HappyShield/happyshield.github.io/index_PT.md

---
layout: page
title: HappyShield
tagline: Curved Crease Origami Face Shield For Infection Control
permalink: /pt/
language: pt
---

<style>.embed-container { position: relative; padding-bottom: 56.25%; height: 0; overflow: hidden; max-width: 100%; } .embed-container iframe, .embed-container object, .embed-container embed { position: absolute; top: 0; left: 0; width: 100%; height: 100%; }</style><div class='embed-container'><iframe src='https://www.youtube.com/embed//NzHtaLhImxM' frameborder='0' allowfullscreen></iframe></div>

---

HappyShieldGif

# What? 

---

HappyShield is a new **open-source** design for a **simple, foldable face shield** for infection control in the context of the Covid-19 pandemic. 

---

# Why?

---

Healthcare workers need face shields in addition to masks and goggles to provide protection from splashes and sprays of infected bodily fluids from Covid-19 patients during a number of high-risk medical procedures and situations. There is currently a **significant shortage of face shields globally**, which is likely to be **particularly severe in less wealthy regions** without the ability to buy or manufacture necessary Personal Protective Equipment (PPE) as easily or quickly as wealthy countries. 

---

# How? 

---

The aim of this project is to develop, disseminate, and mass-manufacture a set of designs for face shields which are **safe**, **cheap**, **easy to mass-produce** quickly using **materials, equipment, and labour available in low and middle-income regions**, are **easy to reuse**, and are **comfortable** enough to be worn for extended periods by healthcare workers without inducing pain or discomfort. The first phase of this project, the development of a prototype design, has yielded **HappyShield**, which successfully meets these design goals. The features of the HappyShield design are listed below:

---

## Features

---

* Single-sheet fluid-impermeable design with **extra protection from fluids and sprays from above**.   

---

* Easy **decontamination for reuse** over high numbers of shifts.   

---

* Form-fitting and adjustable shape allowing for **comfortable wearing for extended periods**.   

---

* **Fast, flexible and scaleable mass-manufacturing approaches** to help meet global demand despite supply chain disruptions.  

---
---

## Gallery

---

<script src="https://snapwidget.com/js/snapwidget.js"></script>
<iframe src="https://snapwidget.com/embed/810063" class="snapwidget-widget" allowtransparency="true" frameborder="0" scrolling="no" style="border:none; overflow:hidden;  width:100%; "></iframe>

---
---

# How can I help? 

---

We have **begun production of HappyShields in the UK**, and are hoping to **rapidly expand** our production and distribution capacity here. Most especially, however, we are **currently seeking partnerships and collaborations** which can help us to disseminate the HappyShield design and related production methods to **less wealthy countries** and jump-start mass-production of face shields there as quickly as possible.

---

### _Here's how you can help:_

---

## 1. 🏭 Manufacturers and Makers

Do you have **access to a laser-cutter, a bench-mounted hydraulic press, die-cutting machinery**, or have connections to an institution or business which does? [We would love to be connected](mailto:natmat@aha.cam.ac.uk?Subject=HappyShield Inquiry: Manufacturing) so that we can help you to **start mass-manufacturing HappyShields locally** as quickly as possible.

Are you a **maker / DIY enthusiast**? We have developed and documented a small number of diverse manufacturing pathways (shown below) for HappyShield, but because of the simplicity of the design, we anticipate there being many effective ways to produce them using locally available materials, equipment, and labor. We need your help to **develop and document these new methods** so that makers and manufacturers worldwide can scale up production using materials and equipment that they already have. All of our [documentation](https://github.com/HappyShield/happyshield.github.io) and [template files](https://github.com/HappyShield/HappyShield) are available open-source on GitHub. Pull requests are encouraged!

---

| Production Method | Web | Print | Video | Templates |
|---|---|---|---|---|
| Hand Creasing | [<i class="em em-iphone" aria-role="presentation" aria-label="MOBILE PHONE"></i>](../hand-creasing/{{page.language}}/) |  [<i class="em em-page_facing_up" aria-role="presentation" aria-label="PAGE FACING UP"></i>](./Instructions/HandCreasing/Assets/Output/InstructionsPDF/Instructions.pdf)  | [<i class="em em-video_camera" aria-role="presentation" aria-label="VIDEO CAMERA"></i>](https://youtu.be/8RvlrtrebBE) | [<i class="em em-triangular_ruler" aria-role="presentation" aria-label="TRIANGULAR RULER"></i>](https://github.com/HappyShield/HappyShield/tree/master/Templates/HandCreasing) |
| Laser-cut + Pressure Creasing | [<i class="em em-iphone" aria-role="presentation" aria-label="MOBILE PHONE"></i>](../pressure-creasing/{{page.language}}/) | [<i class="em em-page_facing_up" aria-role="presentation" aria-label="PAGE FACING UP"></i>](./Instructions/LaserCutAndPressureCreasing/Assets/Output/InstructionsPDF/Instructions.pdf) | [<i class="em em-video_camera" aria-role="presentation" aria-label="VIDEO CAMERA"></i>](https://youtu.be/IPKiPi-Tne8) | [<i class="em em-triangular_ruler" aria-role="presentation" aria-label="TRIANGULAR RULER"></i>](https://github.com/HappyShield/HappyShield/tree/master/Templates/LaserCutAndPressureCreasing)  |
| Laser-cut | [<i class="em em-iphone" aria-role="presentation" aria-label="MOBILE PHONE"></i>](../laser-cut/{{page.language}}/) |  [<i class="em em-page_facing_up" aria-role="presentation" aria-label="PAGE FACING UP"></i>](./Instructions/LaserCut/Assets/Output/InstructionsPDF/Instructions.pdf) | | [<i class="em em-triangular_ruler" aria-role="presentation" aria-label="TRIANGULAR RULER"></i>](https://github.com/HappyShield/HappyShield/tree/master/Templates/LaserCut) |
| Laminated | | | [<i class="em em-video_camera" aria-role="presentation" aria-label="VIDEO CAMERA"></i>](https://youtu.be/yBTCImOzLss) | |
| WaveShield | [<i class="em em-iphone" aria-role="presentation" aria-label="MOBILE PHONE"></i>](../wave-shield/{{page.language}}/) | [<i class="em em-page_facing_up" aria-role="presentation" aria-label="PAGE FACING UP"></i>](./Instructions/WaveShield/Assets/Output/InstructionsPDF/Instructions.pdf) | [<i class="em em-video_camera" aria-role="presentation" aria-label="VIDEO CAMERA"></i>](https://youtu.be/9PSss8W73v0) | [<i class="em em-triangular_ruler" aria-role="presentation" aria-label="TRIANGULAR RULER"></i>](https://github.com/HappyShield/HappyShield/tree/master/Templates/Waveshield)  |

---

## 2. 🏥 Healthcare Workers

---

Are you responsible for **procurement of PPE for healthcare workers** and do you anticipate needing face shields (or know someone who meets these criteria)? [We would love to connect you](mailto:natmat@aha.cam.ac.uk?Subject=HappyShield Inquiry: Healthcare) with manufacturers locally who can produce HappyShields for you. We can send a **pack of 5-10 HappyShields** to you straight away for any necessary testing and approval.

---

## 3. 🌐 Translators

---

Are you comfortable writing technically in a language other than English? We need your help **translating our homepage, instructions, and video captions** into as many languages as possible, so that these designs and manufacturing methods can reach as many people around the world as possible, particularly in less-wealthy regions. **Please sign up as a translator [here](https://forms.gle/9vHc2FbVvhA7nnZM7)**. If you speak a language which we currently need translators for, we will reach out to you! 

---

#### 🙏 **_Thank you and looking forward to connecting!_**

---
---

## Disclaimer

---

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

--- 

#### Project Credits

University of Cambridge, Department of Architecture  
Centre for Natural Material Innovation

University of Queensland, School of Civil Engineering  
Folded Structures Lab  

Wesam Al Asali  
Tom Bashford  
Aurimas Bukauskas  
Mutsuko Grant  
Joe Gattas  
Ana Gatoo  
Yelda Gin  
Will Hawkins  
Millie Hood  
Aftab Jalia  
Antiopi Koronaki  
Jeff Lee  
Ana Maia  
Andy Conway Morris  
Josh Newman  
Daniel Ott  
Michael Ramage  
Darshil Shah  

---

<script src="https://kit.fontawesome.com/688367e949.js" crossorigin="anonymous"></script>
<div class="socialMediaIconsFooter">
        <a href = "https://twitter.com/happy_PPE">
            <i class="fab fa-twitter" style="font-size:24px; color:black; display: inline-block;"></i> 
        </a>
        <a href ="https://www.instagram.com/happyppe/">
            <i class="fab fa-instagram" style="font-size:24px; color:black; display: inline-block;"></i>
        </a>  
        <a href="mailto:natmat@aha.cam.ac.uk?Subject=HappyShield Inquiry">  natmat@aha.cam.ac.uk</a>
</div>
