HappyShield/happyshield.github.io/index_JA.md

---
layout: page
title: HappyShield [DEPRECATED]
tagline: 感染を防ぐための曲線折り紙フェイスシールド
permalink: /ja-DEPRECATED/
language: ja-DEPRECATED
---

<style>.embed-container { position: relative; padding-bottom: 56.25%; height: 0; overflow: hidden; max-width: 100%; } .embed-container iframe, .embed-container object, .embed-container embed { position: absolute; top: 0; left: 0; width: 100%; height: 100%; }</style><div class='embed-container'><iframe src='https://www.youtube.com/embed//NzHtaLhImxM' frameborder='0' allowfullscreen></iframe></div>

---

HappyShieldGif

# このプロジェクトについて

---

# 2020 04 23: Please Note: This translation of the HappyShield homepage is out of date and should not be considered current. Please refer to the [English version of the homepage](https://happyshield.github.io/en/) for the most up to date version.. 

HappyShield（ハッピーシールド）は、Covid-19のパンデミックを受けて新たに立ち上げられた、**簡単に折ることができる**、**オープンソース**のフェイスシールドです。

---

# なぜフェイスシールド?

---

医療従事者は、多数の医療活動のさなかでCovid-19患者からの飛沫感染を防ぐために、マスクやゴーグルだけでなくフェイスシールドも必要としています。現在、**世界規模でフェイスシールドが重大な不足に陥っており**、特に必要な個人用防具 (PPE)を容易には輸入・製造できない裕福でない国々において、状況は深刻になっています。

---

# どうやって解決する? 

---

このプロジェクトの目的は、**安全で**、**安価で**、**大量生産可能が可能で**、**低所得者層でも入手可能な材料と装置によって調達でき**、**簡単に再利用でき**、**痛みやストレスなく医療従事者が付けていられる**ようなフェイスシールドを**作り、普及させ、大量生産する**ことです。このプロジェクトの最初のフェーズとして我々が試作した**HappyShield**は、これらの目標を達成するようにデザインされました。HappyShieldの特徴は以下のようなものです：

---

## 特徴

---

* 顔の前方からだけではなく**上部からの飛沫を防ぐことができる**、1枚のシートでできた液体を透過しない構造

---

* 複数回の使用を想定し、**簡単に洗浄と再利用できる**素材

---

* **長期間の快適な着用が可能**な、着用者に合わせた形状とアジャストが可能な設計

---

* 供給チェーンの混乱の中でも世界的な需要に答えられる、**迅速かつ柔軟に大量生産が可能な**アプローチ

---
---

## ギャラリー

---

<script src="https://snapwidget.com/js/snapwidget.js"></script>
<iframe src="https://snapwidget.com/embed/810063" class="snapwidget-widget" allowtransparency="true" frameborder="0" scrolling="no" style="border:none; overflow:hidden;  width:100%; "></iframe>

---
---

# 私達をお手伝いしていただけませんか? 

---

私達はイギリスで**HappyShieldの生産を開始**しました。そして、イギリスでの生産・配送能力を急いて拡大することに努めています。しかしそれ以上に、HappyShieldと関連する技術を**比較的裕福でない国々**に届け、可能な限り早くフェイスシールドを大量生産するお手伝いをしてくださるパートナーとコラボレーターを探しています。

---

### _こんな皆様の助けを待っています:_

---

## 1. 🏭 製造業者とメイカーの皆様

レーザーカッターや据え付け型の油圧プレス機、型抜き装置をお持ちの皆様、もしくはそのような装置を持つ機関や企業につながりのある皆様。[ぜひ私達にご連絡ください](mailto:natmat@aha.cam.ac.uk?Subject=HappyShield Inquiry: Manufacturing)。皆様が一刻も早くお住まいの地域でHappyShieldを生産できるようにお手伝いいたします。

メイカーの皆様やDIY愛好家の皆様。下にリンクを貼ったように、私達はHappyShieldの生産方法をある程度の種類考え、ドキュメントとしてまとめてきました。しかし、シンプルな設計であることから、各地の皆様の使える材料や設備、労働力によってはもっと効率のよい方法があると考えられます。世界各地のメイカーや生産者が製造スケールを上げるために、皆様にはぜひ**新しい生産手法を見つけ、報告してほしい**と考えています。我々がこれまでにまとめた[ドキュメント](https://github.com/HappyShield/happyshield.github.io)と[テンプレートファイル](https://github.com/HappyShield/HappyShield)はGitHubでオープンソースにて配布されています。ぜひプルリクエストを送ってください！

**問題点と要望**：もしも我々のドキュメントやテンプレートに誤りや不足を発見なさったり、さらなる要望がありましたら、ぜひ我々のGitHubリポジトリにある[Issue](https://help.github.com/en/github/managing-your-work-on-github/creating-an-issue)にご連絡ください。皆様の要望を反映し、皆様にとってなるべく明確で簡単な資料を作っていきたいと考えています。

* [ドキュメントに関するIssueはこちらまで](https://github.com/HappyShield/happyshield.github.io/issues)    
* [テンプレートに関するIssueはこちらまで](https://github.com/HappyShield/HappyShield/issues)  

---

| 生産方法 | ウェブ | 印刷物 | ビデオ | テンプレート |
|---|---|---|---|---|
| Hand Creasing | [<i class="em em-iphone" aria-role="presentation" aria-label="MOBILE PHONE"></i>](../hand-creasing/{{page.language}}/) |  [<i class="em em-page_facing_up" aria-role="presentation" aria-label="PAGE FACING UP"></i>](./Instructions/HandCreasing/Assets/Output/InstructionsPDF/Instructions.pdf)  | [<i class="em em-video_camera" aria-role="presentation" aria-label="VIDEO CAMERA"></i>](https://youtu.be/8RvlrtrebBE) | [<i class="em em-triangular_ruler" aria-role="presentation" aria-label="TRIANGULAR RULER"></i>](https://github.com/HappyShield/HappyShield/tree/master/Templates/HandCreasing) |
| Laser-cut + Pressure Creasing | [<i class="em em-iphone" aria-role="presentation" aria-label="MOBILE PHONE"></i>](../pressure-creasing/{{page.language}}/) | [<i class="em em-page_facing_up" aria-role="presentation" aria-label="PAGE FACING UP"></i>](./Instructions/LaserCutAndPressureCreasing/Assets/Output/InstructionsPDF/Instructions.pdf) | [<i class="em em-video_camera" aria-role="presentation" aria-label="VIDEO CAMERA"></i>](https://youtu.be/IPKiPi-Tne8) | [<i class="em em-triangular_ruler" aria-role="presentation" aria-label="TRIANGULAR RULER"></i>](https://github.com/HappyShield/HappyShield/tree/master/Templates/LaserCutAndPressureCreasing)  |
| Laser-cut | [<i class="em em-iphone" aria-role="presentation" aria-label="MOBILE PHONE"></i>](../laser-cut/{{page.language}}/) |  [<i class="em em-page_facing_up" aria-role="presentation" aria-label="PAGE FACING UP"></i>](./Instructions/LaserCut/Assets/Output/InstructionsPDF/Instructions.pdf) | | [<i class="em em-triangular_ruler" aria-role="presentation" aria-label="TRIANGULAR RULER"></i>](https://github.com/HappyShield/HappyShield/tree/master/Templates/LaserCut) |
| Laminated | | | [<i class="em em-video_camera" aria-role="presentation" aria-label="VIDEO CAMERA"></i>](https://youtu.be/yBTCImOzLss) | |
| WaveShield | [<i class="em em-iphone" aria-role="presentation" aria-label="MOBILE PHONE"></i>](../wave-shield/{{page.language}}/) | [<i class="em em-page_facing_up" aria-role="presentation" aria-label="PAGE FACING UP"></i>](./Instructions/WaveShield/Assets/Output/InstructionsPDF/Instructions.pdf) | [<i class="em em-video_camera" aria-role="presentation" aria-label="VIDEO CAMERA"></i>](https://youtu.be/9PSss8W73v0) | [<i class="em em-triangular_ruler" aria-role="presentation" aria-label="TRIANGULAR RULER"></i>](https://github.com/HappyShield/HappyShield/tree/master/Templates/Waveshield)  |

---

## 2. 🏥 医療従事者

---

医療従事者のためにPPEの調達を行う担当者で、フェイスシールドが必要になると予想される方（もしくはそのような知り合いがいる方）へ。[ぜひ私達にご連絡ください](mailto:natmat@aha.cam.ac.uk?Subject=HappyShield Inquiry: Healthcare)。HappyShieldsを製造することのできる各地域の生産者にお繋ぎします。また、テストや承認プロセスのためのサンプルが必要であれば、5~10個のHappyShieldをお送りします。

---

## 3. 🌐 翻訳者

---

このページを（技術的な正確性を保ちながら）英語以外の言語に翻訳することのできる方はいらっしゃいますか？私達は自分たちの設計・生産の手法をできるだけ多くの人々（とりわけ、比較的裕福ではない地域）に届けたいと考えており、そのためにも可能な限り多くの言語で**ホームページ・制作手順・ビデオ字幕を翻訳する必要があります**。[ここ](https://forms.gle/9vHc2FbVvhA7nnZM7)から登録をして翻訳者になっていただけませんか？。 もしも私達がまだ必要とする言語の翻訳者だとわかった場合には、すぐにご連絡します！

---

#### 🙏 **_一緒に戦いましょう！_**

---
---

## 免責事項 (Disclaimer)

---

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

--- 

#### クレジット

University of Cambridge, Department of Architecture  
Centre for Natural Material Innovation

University of Queensland, School of Civil Engineering  
Folded Structures Lab  

Wesam Al Asali  
Tom Bashford  
Aurimas Bukauskas  
Mutsuko Grant  
Joe Gattas  
Ana Gatoo  
Yelda Gin  
Will Hawkins  
Millie Hood  
Aftab Jalia  
Antiopi Koronaki  
Jeff Lee  
Ana Maia  
Andy Conway Morris  
Josh Newman  
Daniel Ott  
Michael Ramage  
Darshil Shah  

---

<script src="https://kit.fontawesome.com/688367e949.js" crossorigin="anonymous"></script>
<div class="socialMediaIconsFooter">
        <a href = "https://twitter.com/happy_PPE">
            <i class="fab fa-twitter" style="font-size:24px; color:black; display: inline-block;"></i> 
        </a>
        <a href ="https://www.instagram.com/happyppe/">
            <i class="fab fa-instagram" style="font-size:24px; color:black; display: inline-block;"></i>
        </a>  
        <a href="mailto:natmat@aha.cam.ac.uk?Subject=HappyShield Inquiry">  natmat@aha.cam.ac.uk</a>
</div>
