HappyShield/happyshield.github.io/languages.md

---
layout: page
title: 🌐
permalink: /languages/
language: 
---

# [EN](../en) [AR](../ar/) [DE](../de/) [FR](../fr/) [PT](../pt/) [TH](../th/) [TR](../tr/) [ZH](../zh/)
