HappyShield/happyshield.github.io/index_TR.md

---
layout: page
title: HappyShield
tagline: Enfeksiyon Kontrolü İçin Eğimli Katlanan Origami Yüz Siperliği
permalink: /tr/
language: tr
---

<style>.embed-container { position: relative; padding-bottom: 56.25%; height: 0; overflow: hidden; max-width: 100%; } .embed-container iframe, .embed-container object, .embed-container embed { position: absolute; top: 0; left: 0; width: 100%; height: 100%; }</style><div class='embed-container'><iframe src='https://www.youtube.com/embed//NzHtaLhImxM' frameborder='0' allowfullscreen></iframe></div>

---

HappyShieldGif

# Nedir? 

---

HappyShield, Covid-19 salgını bağlamında enfeksiyon kontrolüne yönelik **basit, katlanabilir bir yüz siperliği** için yeni bir **açık kaynaklı** tasarımdır. 

---

# Neden?

---

Sağlık çalışanları, yüksek riskli tıbbi prosedürler ve durumlar sırasında Covid-19 hastalarının enfekte vücut sıvılarının sıçramalarına ve püskürmelerine karşı koruma sağlamak için maskelere ve gözlüklere ek olarak yüz siperliklerine ihtiyaç duyarlar. Şu anda **dünya genelinde önemli bir yüz siperliği sıkıntısı var**. Bu durum, varlıklı ülkeler kadar kolay ya da çabuk şekilde gerekli Kişisel Koruyucu Ekipmanı (KKE) satın alma veya üretme imkanı olmayan  **daha az varlıklı bölgelerde daha ciddi seyredebilir.** 

---

# Nasıl? 

---

Bu projenin amacı,  **güvenli**, **ucuz**, **az ve orta gelirli bölgelerde bulunan malzeme, ekipman ve işçilik** hızlıca kullanılarak **seri üretilmesi kolay**, **yeniden kullanımı kolay** ve sağlık çalışanları tarafından ağrı veya rahatsızlık yaratmadan uzun süre giyilebilecek kadar **rahat** yüz siperlikleri için bir dizi tasarım geliştirmek, yaymak ve seri üretmektir. Bu projenin ilk aşaması olan bir prototip tasarımın geliştirilmesi, bu tasarım hedeflerini başarıyla karşılayan **HappyShield** ile sonuçlanmıştır. HappyShield tasarımının özellikleri aşağıda listelenmiştir:

---

## Özellikler

---

* Tek levhadan **yukarıdan gelen akışkanlara ve püskürmelere karşı ekstra koruma** ile sıvı geçirimsiz tasarım.   

---

* Çok sayıda vardiyada yeniden kullanım için **kolay dekontaminasyon**.   

---

* **Uzun süre rahat kullanım** sağlayan yüze oturan ve ayarlanabilir biçim.   

---

* Tedarik zinciri aksaklıklarına rağmen küresel talebi karşılamaya yardımcı olmak için **hızlı, esnek ve ölçeklendirilebilir seri üretim yaklaşımları**.  

---
---

## Galeri

---

<script src="https://snapwidget.com/js/snapwidget.js"></script>
<iframe src="https://snapwidget.com/embed/810063" class="snapwidget-widget" allowtransparency="true" frameborder="0" scrolling="no" style="border:none; overflow:hidden;  width:100%; "></iframe>

---
---

# Nasıl yardımcı olabilirim? 

---

**İngiltere'de HappyShields üretimine başladık** ve burada üretim ve dağıtım kapasitemizi **hızla genişletmeyi** umuyoruz. Bununla birlikte, özellikle **HappyShield tasarımını ve ilgili üretim yöntemlerini** daha az varlıklı ülkelere yaymak ve oralarda yüz siperliklerinin seri üretimini olabildiğince hızlı bir şekilde yaygınlaştırmak için **şu anda yardımcı olabilecek ortaklıklar ve işbirlikleri** arıyoruz. 

---

### _Şu şekilde yardımcı olabilirsiniz:_

---

## 1. 🏭 Üreticiler ve Makerlar

**Lazer kesici, masa üstü hidrolik pres, kalıp kesme makinesine erişim**'iniz ya da bunları kullanan kurum ya da işletmelerle bağlantınız var mı? Olabildiğince hızlı bir şekilde **Happyshield seri üretimine yerel olarak başlamanıza** yardımcı olabilmek için [iletişime geçmeyi çok isteriz](mailto:natmat@aha.cam.ac.uk?Subject=HappyShield Inquiry: Manufacturing).

**Maker / DIY meraklısı** mısınız? HappyShield için az sayıda çeşitli üretim yolları (aşağıda gösterilmiştir) geliştirdik ve belgeledik, ancak tasarımın basitliği nedeniyle, bunları yerel olarak mevcut malzemeler, ekipman ve işçilik kullanarak üretmenin birçok etkili yolu olduğunu öngörüyoruz. Dünya çapındaki makerların ve üreticilerin halihazırda sahip oldukları malzeme ve ekipmanları kullanarak üretimi artırabilmeleri için **bu yeni yöntemleri geliştirmek ve belgelemek** için yardımınıza ihtiyacımız var. Bütün [belgelerimiz](https://github.com/HappyShield/happyshield.github.io) ve [şablon dosyalarımız](https://github.com/HappyShield/HappyShield) açık kaynak olarak GitHub'da erişime açık. Pull request'leri teşvik ediyoruz!

---

| Üretim Yöntemi | Web | Yazıcı | Video | Şablonlar |
|---|---|---|---|---|
| Elle Katlama | [<i class="em em-iphone" aria-role="presentation" aria-label="MOBILE PHONE"></i>](../hand-creasing/{{page.language}}/) |  [<i class="em em-page_facing_up" aria-role="presentation" aria-label="PAGE FACING UP"></i>](./Instructions/HandCreasing/Assets/Output/InstructionsPDF/Instructions.pdf)  | [<i class="em em-video_camera" aria-role="presentation" aria-label="VIDEO CAMERA"></i>](https://youtu.be/8RvlrtrebBE) | [<i class="em em-triangular_ruler" aria-role="presentation" aria-label="TRIANGULAR RULER"></i>](https://github.com/HappyShield/HappyShield/tree/master/Templates/HandCreasing) |
| Lazer Kesici + Basınçlı Katlama | [<i class="em em-iphone" aria-role="presentation" aria-label="MOBILE PHONE"></i>](../pressure-creasing/{{page.language}}/) | [<i class="em em-page_facing_up" aria-role="presentation" aria-label="PAGE FACING UP"></i>](./Instructions/LaserCutAndPressureCreasing/Assets/Output/InstructionsPDF/Instructions.pdf) | [<i class="em em-video_camera" aria-role="presentation" aria-label="VIDEO CAMERA"></i>](https://youtu.be/IPKiPi-Tne8) | [<i class="em em-triangular_ruler" aria-role="presentation" aria-label="TRIANGULAR RULER"></i>](https://github.com/HappyShield/HappyShield/tree/master/Templates/LaserCutAndPressureCreasing)  |
| Lazer Kesici | [<i class="em em-iphone" aria-role="presentation" aria-label="MOBILE PHONE"></i>](../laser-cut/{{page.language}}/) |  [<i class="em em-page_facing_up" aria-role="presentation" aria-label="PAGE FACING UP"></i>](./Instructions/LaserCut/Assets/Output/InstructionsPDF/Instructions.pdf) | | [<i class="em em-triangular_ruler" aria-role="presentation" aria-label="TRIANGULAR RULER"></i>](https://github.com/HappyShield/HappyShield/tree/master/Templates/LaserCut) |
| Laminasyon | | | [<i class="em em-video_camera" aria-role="presentation" aria-label="VIDEO CAMERA"></i>](https://youtu.be/yBTCImOzLss) | |
| WaveShield | [<i class="em em-iphone" aria-role="presentation" aria-label="MOBILE PHONE"></i>](../wave-shield/{{page.language}}/) | [<i class="em em-page_facing_up" aria-role="presentation" aria-label="PAGE FACING UP"></i>](./Instructions/WaveShield/Assets/Output/InstructionsPDF/Instructions.pdf) | [<i class="em em-video_camera" aria-role="presentation" aria-label="VIDEO CAMERA"></i>](https://youtu.be/9PSss8W73v0) | [<i class="em em-triangular_ruler" aria-role="presentation" aria-label="TRIANGULAR RULER"></i>](https://github.com/HappyShield/HappyShield/tree/master/Templates/Waveshield)  |

---

## 2. 🏥 Sağlık Çalışanları

---

**Sağlık çalışanları için KKD tedariki**nden mi sorumlusunuz ve yüz siperliklerine ihtiyaç duyulduğunu mu tahmin ediyorsunuz (veya bu kriterleri karşılayan birini mi tanıyorsunuz)? Sizi sizin için yerel olarak HappyShield üretebilecek üreticilerle [iletişime geçirmeyi çok isteriz](mailto:natmat@aha.cam.ac.uk?Subject=HappyShield Inquiry: Healthcare). Gerekli herhangi bir test ve onay için **5-10 HappyShield içeren bir paket**i size hemen gönderebiliriz.

---

## 3. 🌐 Çevirmenler

---

Teknik olarak İngilizce dışında bir dilde rahat yazabilir misiniz? Bu tasarımların ve üretim yöntemlerinin dünyada, özellikle de daha az varlıklı bölgelerde, mümkün olduğunca çok insana ulaşabilmesi için **ana sayfamızı, talimatlarımızı ve video altyazılarımızı** mümkün olduğunca çok dile çevirmek için yardımınıza ihtiyacımız var.  **Çevirmenlik için lütfen [buradan](https://forms.gle/9vHc2FbVvhA7nnZM7)** kayıt olunuz. Şu anda çevirmenlere ihtiyaç duyduğumuz bir dili konuşuyorsanız, sizinle iletişime geçeceğiz! 

---

#### 🙏 **_Teşekkürler ve iletişime geçmek için sabırsızlanıyoruz!_**

---
---

## Sorumluluk Reddi

---

Cambridge Üniversitesi (UC) ve Queensland Üniversitesi (UQ), HappyShield'ın tasarımı, özellikleri, dayanıklılığı, uygun kullanımı veya performansı hakkında, satılabilirlik ve belirli bir amaca uygunluk hakkındaki zımni garantiyle sınırlı kalmamak üzere, açık veya zımni hiçbir garanti vermemektedir.  HappyShield, sıvılara ve spreylere maruz kalmayı en aza indirecek şekilde tasarlanmıştır, ancak UC ve UQ, HappyShield'ın kullanıcıları COVID-19 enfeksiyonundan veya başka bulaşıcı hastalıklardan koruyacağını garanti etmez. Bu materyaldeki hiçbir şey tıbbi tavsiye oluşturmaz ve kullanıcılar HappyShield'in amaçladıkları kullanıma uygun olup olmadığı ve diğer tıbbi veya başka türden stratejilerle birlikte kullanmaları gerekip gerekmediği konusunda kendi tıbbi tavsiyelerini takip etmelidirler. Yasaların izin verdiği azami ölçüde, UC ve UQ tüm zımni garantileri, güvenceleri, şartları ve koşulları hariç tutar. UC ve UQ, HappyShield'ın kullanımından kaynaklanan mülki hasar, bedensel yaralanma veya hastalık, ölüm, dolaylı, özel veya buna bağlı zararlar (“Talepler”) dahil ancak bunlarla sınırlı olmamak üzere herhangi bir hak, talep, hasar veya yaralanmadan sorumlu değildir, ve HappyShield kullanıcıları UC ve UQ'yu ve memurlarını, çalışanlarını, yüklenicilerini ve temsilcilerini tüm Taleplerden muaf tutar.

--- 

#### Katkıda Bulunanlar

University of Cambridge, Department of Architecture  
Centre for Natural Material Innovation

University of Queensland, School of Civil Engineering  
Folded Structures Lab  

Wesam Al Asali  
Tom Bashford  
Aurimas Bukauskas  
Mutsuko Grant  
Joe Gattas  
Ana Gatoo  
Yelda Gin  
Will Hawkins  
Millie Hood  
Aftab Jalia  
Antiopi Koronaki  
Jeff Lee  
Ana Maia  
Andy Conway Morris  
Josh Newman  
Daniel Ott  
Michael Ramage  
Darshil Shah  

---

<script src="https://kit.fontawesome.com/688367e949.js" crossorigin="anonymous"></script>
<div class="socialMediaIconsFooter">
        <a href = "https://twitter.com/happy_PPE">
            <i class="fab fa-twitter" style="font-size:24px; color:black; display: inline-block;"></i> 
        </a>
        <a href ="https://www.instagram.com/happyppe/">
            <i class="fab fa-instagram" style="font-size:24px; color:black; display: inline-block;"></i>
        </a>  
        <a href="mailto:natmat@aha.cam.ac.uk?Subject=HappyShield Inquiry">  natmat@aha.cam.ac.uk</a>
</div>
