HappyShield/happyshield.github.io/index_AR.md

---
layout: page
title: HappyShield
tagline: غطاء للوجه قابل للطي 
permalink: /ar/
language: ar
textdirection: rtl
---

<style>.embed-container { position: relative; padding-bottom: 56.25%; height: 0; overflow: hidden; max-width: 100%; } .embed-container iframe, .embed-container object, .embed-container embed { position: absolute; top: 0; left: 0; width: 100%; height: 100%; }</style><div class='embed-container'><iframe src='https://www.youtube.com/embed//NzHtaLhImxM' frameborder='0' allowfullscreen></iframe></div>

---

HappyShieldGif

# ماذا؟ 

---

 HappyShield هو تصميم جديد مفتوح المصدر لدرع وجه بسيط وقابل للطي للتحكم في العدوى في سياق جائحة Covid-19.

---

# لماذا ؟

---

يحتاج العاملون في مجال الرعاية الصحية إلى واقيات للوجه بالإضافة إلى الأقنعة والنظارات الواقية لتوفير الحماية من الرذاذ والبقع للسوائل الجسدية  التي قد تخرج من مرضى Covid-19 خلال الاجراءات الطبية عالية. يوجد حاليًا **نقص كبير في أغطية الوجه على مستوى العالم** ، والتي من المرجح أن تكون شديدة بشكل خاص في **المناطق التي لا تملك المصادر الكافية والقدرة على شراء أو تصنيع معدات الحماية الشخصية الضرورية** (PPE) كما تفعل العديد من الدول حالياً

---

# كيف؟

---

الهدف من هذا المشروع هو تطوير ونشر وتصنيع مجموعة من التصميمات الواقية للوجه التي تكون **آمنة ورخيصة وسهلة الإنتاج بكميات كبيرة بسرعة باستخدام المواد والمعدات والعمالة المتاحة في كل البلدان وخصوصاً تلك ذات الدخل  المنخفض والمتوسط.** نتطلع إلى أغطية وجه يسهل إعادة استخدامها ، وهي **مريحة** بما يكفي لارتدائها لفترات طويلة من قبل العاملين في مجال الرعاية الصحية دون التسبب بالألم أو الانزعاج. أسفرت المرحلة الأولى من هذا المشروع ، وهي تطوير تصميم النموذج الأولي ، عن إنتاج HappyShield الذي حقق أهداف التصميم هذه بنجاح. يتم سرد ميزات تصميم HappyShield أدناه:

---

## المميزات

---

* **تصميم من ورقة واحدة غير منفذة للسوائل مع **حماية إضافية من السوائل والرذاذ من الأعلى

---

* أمكانية **الغسل و إزالة التلوث** بسهولة **لإعادة استخدامها**

---

* شكل مناسب وقابل للتعديل يسمح بارتداء **مريح لفترات طويلة**  

---

* **نهج تصنيع جماعي سريع ومرن وقابل للتطوير** للمساعدة في تلبية الطلب العالمي  

---
---

## صالة عرض

---

<script src="https://snapwidget.com/js/snapwidget.js"></script>
<iframe src="https://snapwidget.com/embed/810063" class="snapwidget-widget" allowtransparency="true" frameborder="0" scrolling="no" style="border:none; overflow:hidden;  width:100%; "></iframe>

---
---

# كيف يمكنني أن أقدم المساعدة؟ 

---

لقد بدأنا في **إنتاج HappyShields في المملكة المتحدة** ، ونأمل في توسيع قدرتنا على الإنتاج والتوزيع بسرعة. ومع ذلك ، نحن نسعى بشكل خاص حاليًا إلى شراكات وتعاون يمكن أن تساعدنا في نشر تصميم HappyShield إلى **البلدان الأقل ثراء و التي بحاجة لأغطية وجه**  والبدء في الإنتاج الجماعي للدروع الواقية هناك بأسرع ما يمكن.

---

### _إليك كيفية المساعدة:_

---

## 1. 🏭 المصنعين والورشات

هل لديك إمكانية الوصول إلى قاطع الليزر ، أو مكبس هيدروليكي، أو آلات قطع القوالب ، أو لديك اتصالات بمؤسسة أو شركة تعمل؟ [نود أن نكون على اتصال](mailto:natmat@aha.cam.ac.uk?Subject=HappyShield Inquiry: Manufacturing) حتى نتمكن من مساعدتك في بدء **تصنيع HappyShields بكميات كبيرة محليًا بأسرع وقت ممكن**

Aهل أنت متحمس **لصنع القناع يدويا ؟** لقد طورنا ووثقنا عددًا صغيرًا من مسارات التصنيع المتنوعة (كما هو موضح أدناه) لـ HappyShield ، ولكن نظرًا لبساطة التصميم ، نتوقع وجود العديد من الطرق الفعالة لإنتاجها باستخدام المواد والمعدات والعمالة المتاحة محليًا. نحن بحاجة لمساعدتكم **لتطوير وتوثيق هذه الأساليب الجديدة** حتى يتمكن المصنعون والمصنعون في جميع أنحاء العالم من زيادة الإنتاج باستخدام المواد والمعدات التي لديهم بالفعل. تتوفر جميع  [ملفات الوثائق](https://github.com/HappyShield/happyshield.github.io) و [المخططات](https://github.com/HappyShield/HappyShield)  مفتوحة المصدر على موقع GitHub

---

| Production Method | Web | Print | Video | Templates |
|---|---|---|---|---|
| الحز اليدوي | [<i class="em em-iphone" aria-role="presentation" aria-label="MOBILE PHONE"></i>](../hand-creasing/{{page.language}}/) |  [<i class="em em-page_facing_up" aria-role="presentation" aria-label="PAGE FACING UP"></i>](./Instructions/HandCreasing/Assets/Output/InstructionsPDF/Instructions.pdf)  | [<i class="em em-video_camera" aria-role="presentation" aria-label="VIDEO CAMERA"></i>](https://youtu.be/8RvlrtrebBE) | [<i class="em em-triangular_ruler" aria-role="presentation" aria-label="TRIANGULAR RULER"></i>](https://github.com/HappyShield/HappyShield/tree/master/Templates/HandCreasing) |
| قص الليزر + الكبس | [<i class="em em-iphone" aria-role="presentation" aria-label="MOBILE PHONE"></i>](../pressure-creasing/{{page.language}}/) | [<i class="em em-page_facing_up" aria-role="presentation" aria-label="PAGE FACING UP"></i>](./Instructions/LaserCutAndPressureCreasing/Assets/Output/InstructionsPDF/Instructions.pdf) | [<i class="em em-video_camera" aria-role="presentation" aria-label="VIDEO CAMERA"></i>](https://youtu.be/IPKiPi-Tne8) | [<i class="em em-triangular_ruler" aria-role="presentation" aria-label="TRIANGULAR RULER"></i>](https://github.com/HappyShield/HappyShield/tree/master/Templates/LaserCutAndPressureCreasing)  |
| قطع ليزر | [<i class="em em-iphone" aria-role="presentation" aria-label="MOBILE PHONE"></i>](../laser-cut/{{page.language}}/) |  [<i class="em em-page_facing_up" aria-role="presentation" aria-label="PAGE FACING UP"></i>](./Instructions/LaserCut/Assets/Output/InstructionsPDF/Instructions.pdf) | | [<i class="em em-triangular_ruler" aria-role="presentation" aria-label="TRIANGULAR RULER"></i>](https://github.com/HappyShield/HappyShield/tree/master/Templates/LaserCut) |
| باستخدام ادوات التغليف | | | [<i class="em em-video_camera" aria-role="presentation" aria-label="VIDEO CAMERA"></i>](https://youtu.be/yBTCImOzLss) | |
| WaveShield | [<i class="em em-iphone" aria-role="presentation" aria-label="MOBILE PHONE"></i>](../wave-shield/{{page.language}}/) | [<i class="em em-page_facing_up" aria-role="presentation" aria-label="PAGE FACING UP"></i>](./Instructions/WaveShield/Assets/Output/InstructionsPDF/Instructions.pdf) | [<i class="em em-video_camera" aria-role="presentation" aria-label="VIDEO CAMERA"></i>](https://youtu.be/9PSss8W73v0) | [<i class="em em-triangular_ruler" aria-role="presentation" aria-label="TRIANGULAR RULER"></i>](https://github.com/HappyShield/HappyShield/tree/master/Templates/Waveshield)  |

---

## 2. 🏥 عمال الرعاية الصحية

---

هل أنت مسؤول عن **شراء معدات الوقاية الشخصية** للعاملين في مجال الرعاية الصحية وهل تتوقع أن تحتاج إلى دروع للوجه (أو تعرف شخصًا يستوفي هذه المعايير)؟ [ نود أن](mailto:natmat@aha.cam.ac.uk?Subject=HappyShield Inquiry: Healthcare) نوصلك بالمصنِّعين محليًا الذين يمكنهم إنتاج HappyShields لك. يمكننا إرسال **عينة من 5-10 HappyShields إليك فورًا** لإجراء أي اختبار أو موافقة ضرورية.

---

## 3. 🌐 المترجمون

---

هل أنت مرتاح في الكتابة من الناحية الفنية بلغة غير الإنجليزية؟ نحتاج إلى مساعدتك في ترجمة الصفحة الرئيسية والتعليمات وتسميات الفيديو إلى أكبر عدد ممكن من اللغات ، بحيث يمكن لهذه التصميمات وأساليب التصنيع الوصول إلى أكبر عدد ممكن من الأشخاص حول العالم ، لا سيما في المناطق الأقل ثراءً. يرجى الاشتراك كمترجم  [هنا](https://forms.gle/9vHc2FbVvhA7nnZM7)**.  إذا كنت تتحدث لغة نحتاج حاليًا إلى مترجمين لها ، فسنتواصل معك! 

---

#### 🙏 **_🙏 شكرا لكم ونتطلع إلى التواصل!_**

---
---

## Disclaimer اخلاء مسؤولية

---

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

--- 

#### Project Credits حقوق المشروع وفريق العمل

University of Cambridge, Department of Architecture  
Centre for Natural Material Innovation

University of Queensland, School of Civil Engineering  
Folded Structures Lab  

Wesam Al Asali  
Tom Bashford  
Aurimas Bukauskas  
Mutsuko Grant  
Joe Gattas  
Ana Gatoo  
Yelda Gin  
Will Hawkins  
Millie Hood  
Aftab Jalia  
Antiopi Koronaki  
Jeff Lee  
Ana Maia  
Andy Conway Morris  
Josh Newman  
Daniel Ott  
Michael Ramage  
Darshil Shah  

---

<script src="https://kit.fontawesome.com/688367e949.js" crossorigin="anonymous"></script>
<div class="socialMediaIconsFooter">
        <a href = "https://twitter.com/happy_PPE">
            <i class="fab fa-twitter" style="font-size:24px; color:black; display: inline-block;"></i> 
        </a>
        <a href ="https://www.instagram.com/happyppe/">
            <i class="fab fa-instagram" style="font-size:24px; color:black; display: inline-block;"></i>
        </a>  
        <a href="mailto:natmat@aha.cam.ac.uk?Subject=HappyShield Inquiry">  natmat@aha.cam.ac.uk</a>
</div>
