HappyShield/happyshield.github.io/assets/images/HS_Concept_00_NonLooping2xSlower.gif

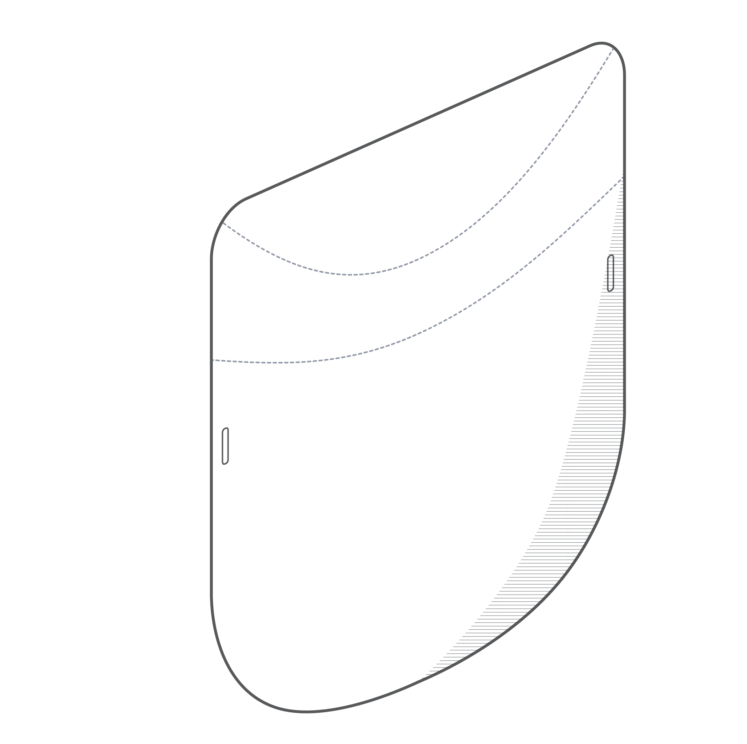
assets/images/HS_Concept_00_NonLooping2xSlower.gif
