HappyShield/happyshield.github.io/Instructions/UniversalAssets/Materials/HS_FP_Alcohol0.jpg

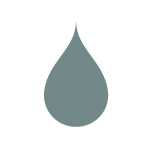
Instructions/UniversalAssets/Materials/HS_FP_Alcohol0.jpg
