HappyShield/happyshield.github.io/Instructions/UniversalAssets/Materials/HS_FP_Band.jpg

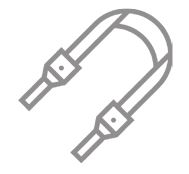
Instructions/UniversalAssets/Materials/HS_FP_Band.jpg
