HappyShield/happyshield.github.io/Instructions/UniversalAssets/Materials/HS_FP_MDF.jpg

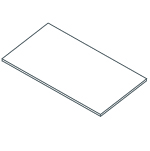
Instructions/UniversalAssets/Materials/HS_FP_MDF.jpg
