HappyShield/happyshield.github.io/Instructions/UniversalAssets/Materials/HS_FP_PET.jpg

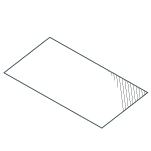
Instructions/UniversalAssets/Materials/HS_FP_PET.jpg
