HappyShield/happyshield.github.io/Instructions/UniversalAssets/Materials/HS_FP_Tape.jpg

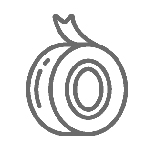
Instructions/UniversalAssets/Materials/HS_FP_Tape.jpg
