HappyShield/happyshield.github.io/Instructions/HandCreasing/handCreasing_PT.md

---
layout: page
title: Vincar Manualmente
tagline: &nbsp <span class="instructionsTaglineEmojiLinks"> <a href="https://youtu.be/8RvlrtrebBE"><i class="em em-video_camera" aria-role="presentation" aria-label="VIDEO CAMERA"></i></a> <a href = "https://github.com/HappyShield/HappyShield/tree/master/Templates/HandCreasing" ><i class="em em-triangular_ruler" aria-role="presentation" aria-label="TRIANGULAR RULER"></i></a></span>
permalink: /hand-creasing/pt/
language: pt
---

<i class="em em-timer_clock" aria-role="presentation" aria-label=""></i>: 10-15′

---

<script src="https://snapwidget.com/js/snapwidget.js"></script>
<iframe src="https://snapwidget.com/embed/810064" class="snapwidget-widget" allowtransparency="true" frameborder="0" scrolling="no" style="border:none; overflow:hidden;  width:100%; "></iframe>

---

---

## Aviso Legal (Disclaimer)

---

The University of Cambridge (UC) and the University of Queensland (UQ) make no warranty of any kind, express or implied, about the design, characteristics, durability, proper use or performance of the HappyShield, including but not limited to implied warranties of merchantability and fitness for any particular purpose. The HappyShield is designed to minimise exposure to fluids and sprays, but UC and UQ do not warrant that HappyShield will protect users from COVID-19 infection or any other infectious disease. Nothing in this material constitutes medical advice, and users should seek their own medical advice about whether HappyShield is suitable for the use they intend, and whether they should use it in conjunction with any other medical or other strategies. To the fullest extent allowed by law, UC and UQ exclude all implied warranties, guarantees, terms and conditions. UC and UQ are not liable for any claims, demands, damages or injuries, including but not limited to property damage, bodily injury or illness, death, indirect, special or consequential damages (“the Claims”) arising out of using the HappyShield, and users of HappyShield release UC and UQ and their officers, employees, contractors and agents from all Claims.

---

--- 

## Ferramentas

---

* Tesoura ou lâmina de corte
* Caneta esferográfica
* Régua
* Faca de manteiga
* Impressora

---

## Materiais

---

**Viseira**

* Polietileno tereftalato (PET) com 0,5 mm de espessura ou como alternativa uma folha de acetato 
* Fita elástica larga de 20 mm (70% poliéster 30% borracha)
* Fita adesiva

---

---

# Instruções

---

# 1 



Descarrege o modelo de vinco. Modelos de tamanho A4 estão disponíveis para viseiras de tamanho A3. Modelos de tamanho "tipo carta" estão disponíveis para viseiras de tamanho "tipo tablóide". Se não tiver acesso a uma impressora, pode desenhar o seu próprio modelo usando as dimensões ilustradas acima.

---

# 2



Coloque a folha transparente em cima do modelo. Marque a localização dos furos de cinta com a caneta ou marcador. Não se preocupe com a tinta, pode ser removida posteriormente com um pano embebido em álcool.  

---

# 3



Trace os limites da viseira para cortar. 

---

# 4



Corte os limites da viseira usando a tesoura ou a lâmina de corte. Corte os furos de cinta. Também pode usar um furador para fazer estes furos. 

Em seguida, corte os clipes de fricção usando a lâmina de corte.

Agora, vamos desenhar um sorriso!

---

## Método de Decalque A

---

# 5A



Coloque a folha transparente em cima do modelo. Fixe com clips ou fita adesiva para um traçado mais preciso.

---

# 6A



Usando a régua, e aplicando pressão, vinque as linhas entre cada ponto consecutivo, usando 2-3 golpes até ser visível um vinco na folha.

---

# 7A



Vire a folha transparente.  Fixe a folha e o modelo novamente.

---

# 8A



Trace a segunda curva da mesma forma que no passo **6A**.

---

## Método de Decalque B

---

# 5B	



Trace as curvas dobráveis com a caneta (aqui não é necessária pressão adicional). Se desejar, fixe a folha ao modelo com clipes ou fita adesiva para um traçado mais preciso.

---

# 6B



Encontre uma ranhura de 2-5 mm de largura, 2-3 mm de profundidade e pelo menos 5 cm de comprimento numa superfície imóvel ou mesa de trabalho. Ranhuras entre tábuas de chão, segmentos de uma mesa de jantar ou balcão de cozinha funcionam bem para este método. Alternativamente, faça a sua prórpia ranhura num pedaço de madeira ou outro material. Em seguida, utilize a caneta esferográfica ou outra ferramenta com uma ponta não cortante (faca de manteiga, colher ou pauzinho de comida chinesa podem resultar também). 

Usando uma mão mova a folha como se tratasse de um pedaço de tecido numa máquina de costura, use a outra mão para repetidamente percorrer a ferramenta de vinco sobre a superfície do material ao longo da ranhura, seguindo uma das curvas dobráveis que traçou.

---

# 7B



Vire a folha ao contrário.

---

# 8B



Repida o passo 6B para a outra curva dobrável.

---

# 9



Começando numa ponta da curva dobrável, e lentamente até à outra ponta, aperte gentilmente a folha para a dobrar ao longo da curva. Se alguns segmentos não dobrarem fácilmente, repita o precesso de vinco. 

---

# 10



Repita o passo 9 para a outra curva, mas desta vez, dobre a folha na direção contrária. 

---

# 11	



Passe o elástico pelos clipes de fricção. Passe os clipes de fricção pelos orifícios na viseira de trás para a frente.
