HappyShield/happyshield.github.io/Instructions/UniversalAssets/Tools/HS_FP_Press0.jpg

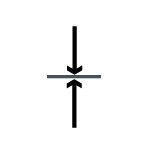
Instructions/UniversalAssets/Tools/HS_FP_Press0.jpg
